clement0909472/silent-mic/cad/out/v2-compact/whisper-mask-v2-compact-divider.step

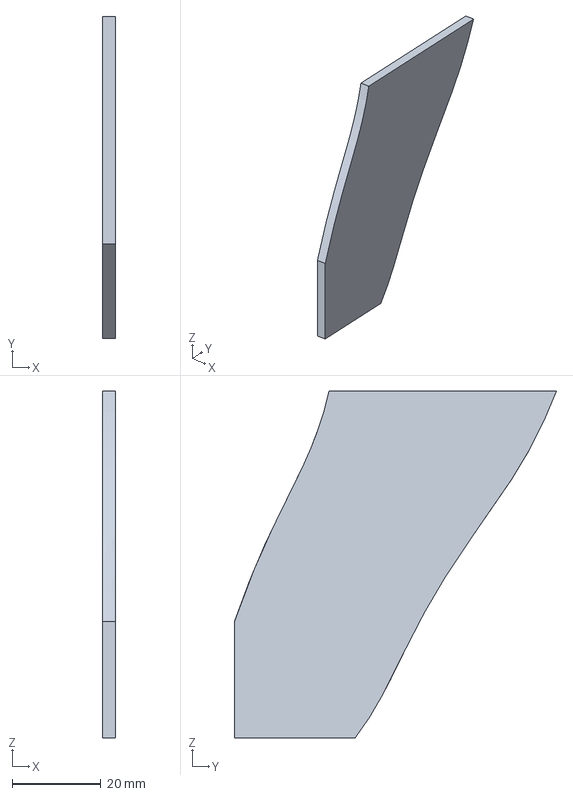
[picture p17: CAD file, 2026-09-09]
cad/out/v2-compact/whisper-mask-v2-compact-divider.step
3.00 x 72.4 x 78.0 mm
