clement0909472/silent-mic/cad/out/v2-compact/whisper-mask-v2-compact-print-plate.stl

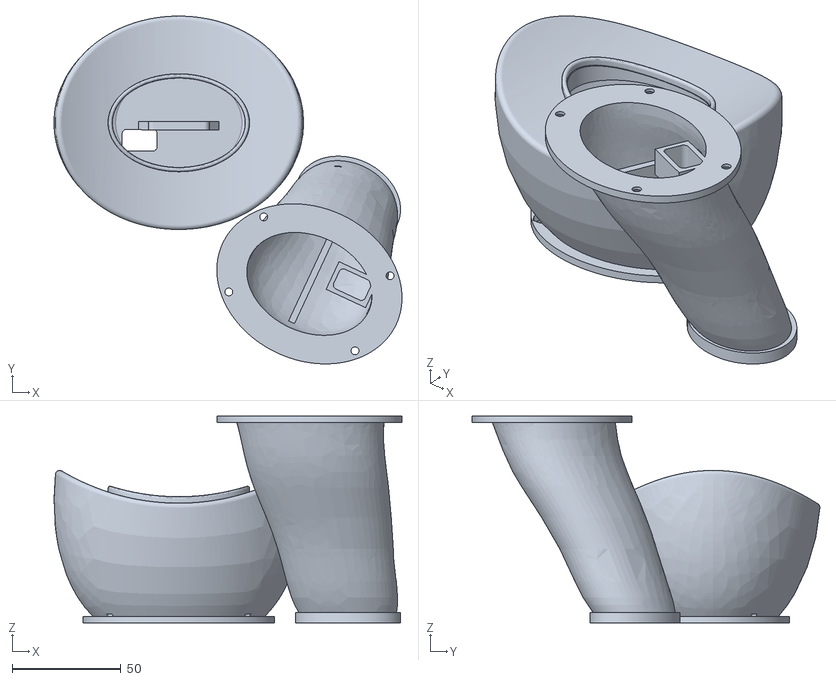
[picture p18: CAD file, 2026-09-09]
cad/out/v2-compact/whisper-mask-v2-compact-print-plate.stl
159.9 x 159.8 x 95.0
