clement0909472/silent-mic/cad/out/v2-compact/11-dji-usb-c-dongle.step

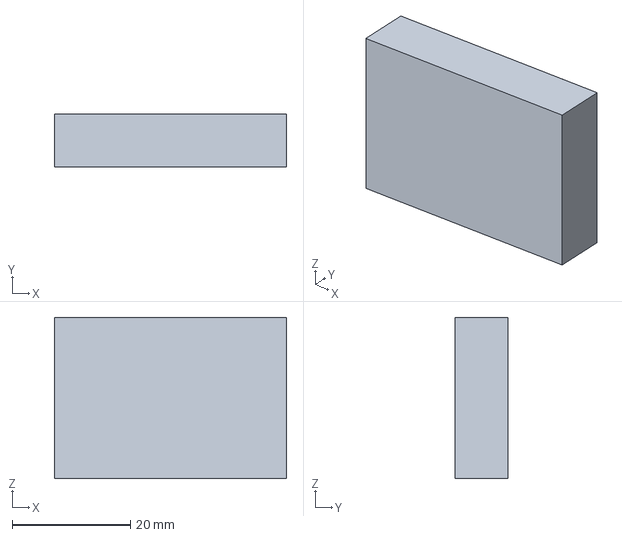
[picture p19: CAD file, 2026-09-09]
cad/out/v2-compact/11-dji-usb-c-dongle.step
39.3 x 8.97 x 27.3 mm
